particitae/pluviometre/Fichiers_Solidworks/corps.SLDPRT

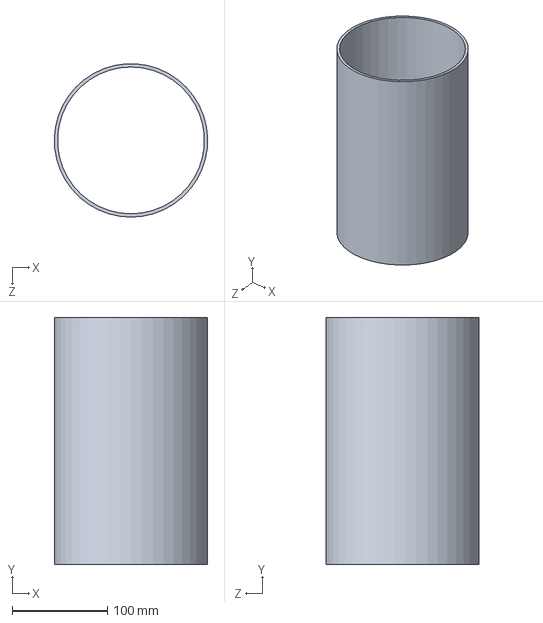
[picture p16: CAD file, 2018-03-17]
Fichiers_Solidworks/corps.SLDPRT
161.4 x 260.0 x 161.3 mm
