particitae/pluviometre/Fichiers_Solidworks/boutier servo.SLDPRT

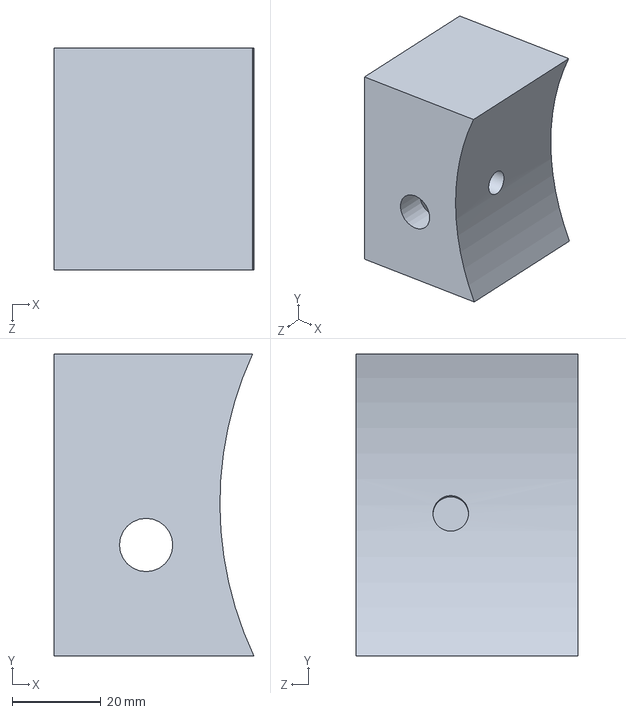
[picture p17: CAD file, 2018-03-17]
Fichiers_Solidworks/boutier servo.SLDPRT
45.0 x 68.0 x 50.0 mm
