particitae/pluviometre/Fichiers_Solidworks/manchon bas.SLDPRT

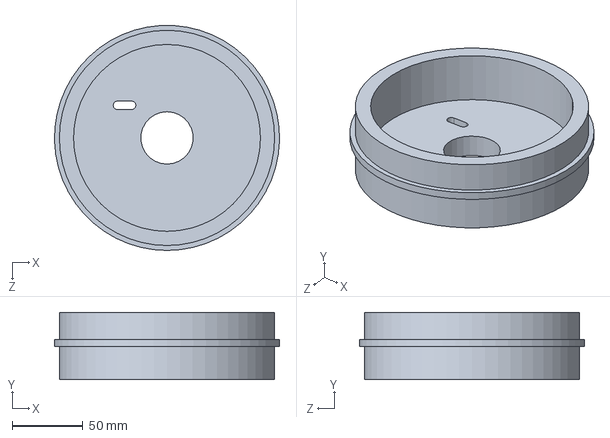
[picture p18: CAD file, 2018-03-17]
Fichiers_Solidworks/manchon bas.SLDPRT
158.9 x 47.5 x 158.9 mm
