particitae/pluviometre/Fichiers_Solidworks/levier servo.SLDPRT

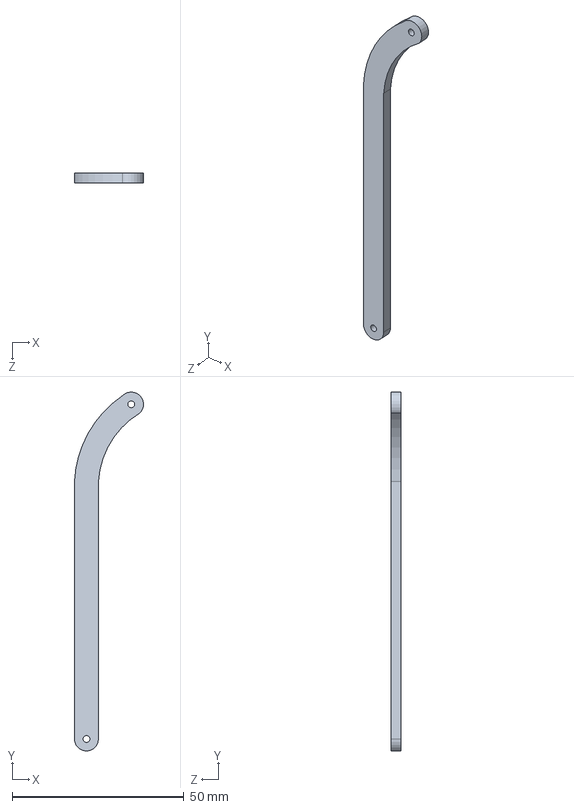
[picture p19: CAD file, 2018-03-17]
Fichiers_Solidworks/levier servo.SLDPRT
20.1 x 104.6 x 3.00 mm
