particitae/pluviometre/Fichiers_Solidworks/bouchon robinet.SLDPRT

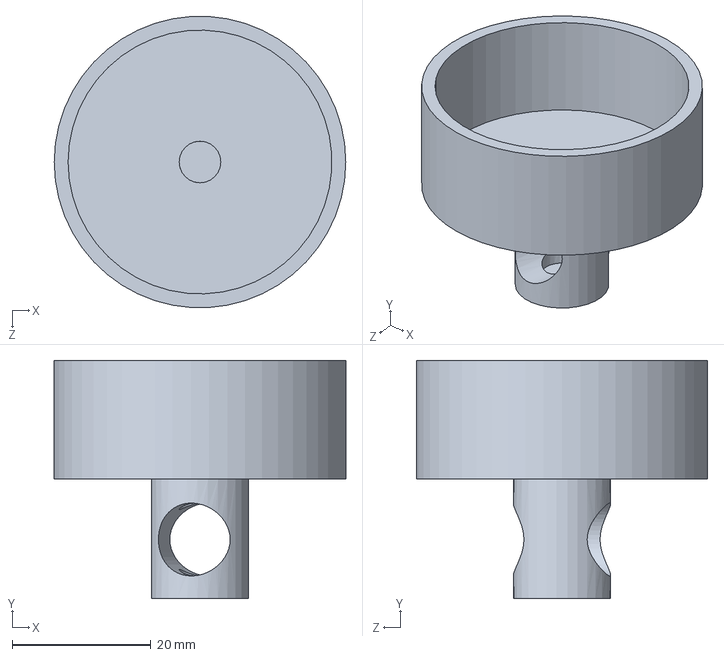
[picture p20: CAD file, 2018-03-17]
Fichiers_Solidworks/bouchon robinet.SLDPRT
42.0 x 34.3 x 41.9 mm
