particitae/pluviometre/Fichiers_Solidworks/manchon.SLDPRT

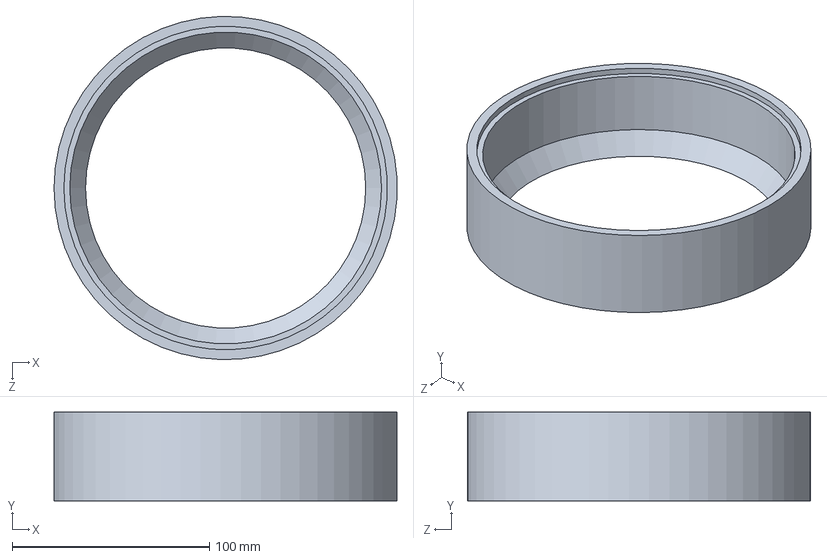
[picture p21: CAD file, 2018-03-17]
Fichiers_Solidworks/manchon.SLDPRT
173.8 x 45.0 x 173.9 mm
